aentinger/BinaryWatchShield/images/binary-watch-shield-action-large.JPG

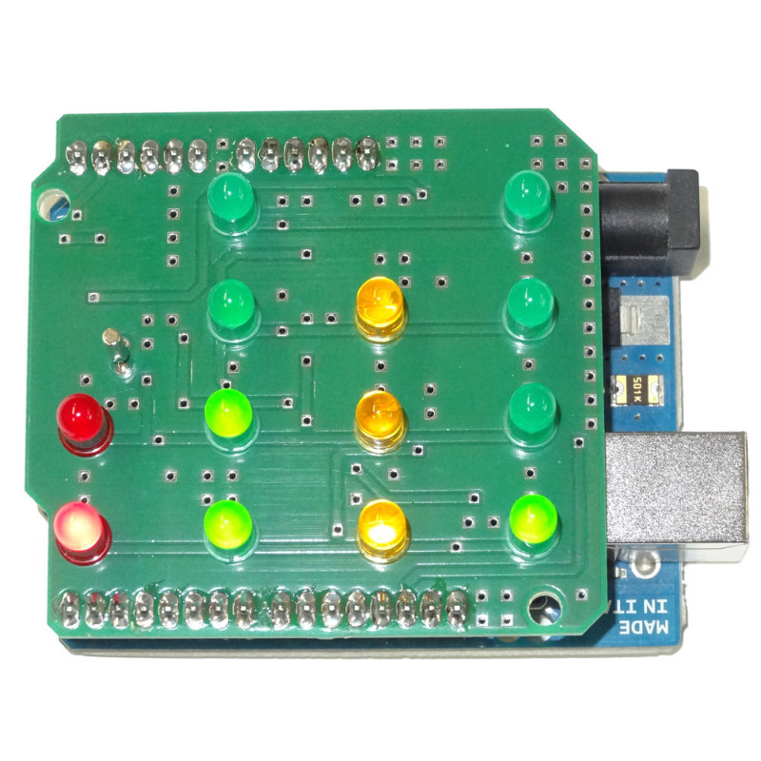
images/binary-watch-shield-action-large.JPG
